FreeFa11/MotionX/Hardware/Simulation/Schematic.asc

C1: cap; 16n
C2: cap; 100p
D1: diode; 1N4148
I1: current; SINE(0 1u 2k 1m)
L1: ind; 500µ
Q1: npn3; 2N2222A
R1: res; 40
R2: res; 1k
R3: res; 5k
R4: res; 5k
R5: res; 5k
R6: res; 5k
R7: res; 4.7k
R8: res; 100Meg
R9: res; {PotB}
R10: res; {PotA}
R11: res; 1.5Meg
R12: res; 15k
R13: res; 4.7k
R14: res; 22k
R15: res; 4.7k
R16: res; 22k
U1: Op-Amp; LM324
U2: Op-Amp; LM324
U3: Op-Amp; LM324
U4: Op-Amp; LM324
U5: Op-Amp; LM324
V1: voltage; 3.3
V2: voltage; PULSE(0 3.3 0 10u 10u 1m 2m)
V3: voltage; SINE(1.65 1 500)
Named nets: 0, +Vcc, Vmotor, Vhall, Vpot, Vpotbuffer
.tran 0.01
Piezo Model
Charge Amplifier
.SUBCKT LM324    1 2 3 4 5
 
  C1   11 12 5.544E-12
  C2    6  7 20.00E-12
  DC    5 53 DX
  DE   54  5 DX
  DLP  90 91 DX
  DLN  92 90 DX
  DP    4  3 DX
  EGND 99  0 POLY(2) (3,0) (4,0) 0 .5 .5
  FB    7 99 POLY(5) VB VC VE VLP VLN 0 15.91E6 -20E6 20E6 20E6 -20E6
  GA    6  0 11 12 125.7E-6
  GCM   0  6 10 99 7.067E-9
  IEE   3 10 DC 10.04E-6
  HLIM 90  0 VLIM 1K
  Q1   11  2 13 QX
  Q2   12  1 14 QX
  R2    6  9 100.0E3
  RC1   4 11 7.957E3
  RC2   4 12 7.957E3
  RE1  13 10 2.773E3
  RE2  14 10 2.773E3
  REE  10 99 19.92E6
  RO1   8  5 50
  RO2   7 99 50
  RP    3  4 30.31E3
  VB    9  0 DC 0
  VC 3 53 DC 2.100
  VE   54  4 DC .6
  VLIM  7  8 DC 0
  VLP  91  0 DC 40
  VLN   0 92 DC 40
.MODEL DX D(IS=800.0E-18)
.MODEL QX PNP(IS=800.0E-18 BF=250)
.ENDS
.param Slide=30
.param PotSize=10k
.param PotA PotSize*Slide/100
.param potB (100-Slide)*PotSize/100
Charge Bias Potentiometer
Motor
Hall Amplifier
LM324 has 20mA of typical output current
We dont know the accurate model of our Piezoelectric Model
which is required for determining the gain from amplifier
Testing Setup
Actual Implementation
